DiomKBS/Diom-75TK-legacy/Backplate/depositphotos_342383522-stock-illus.webp

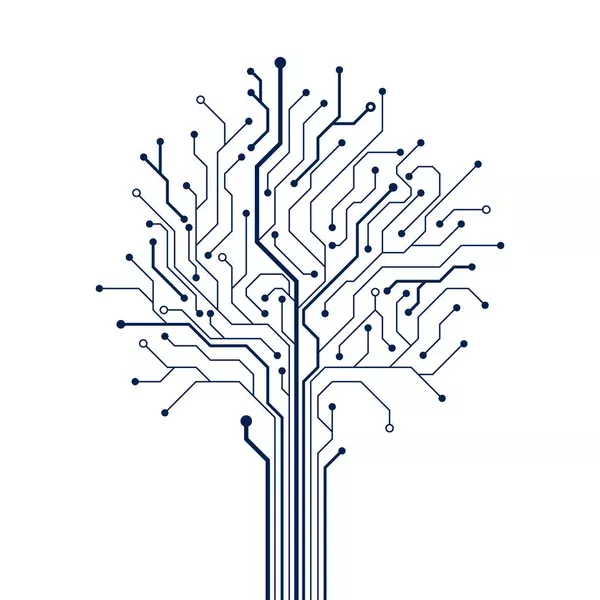
Backplate/depositphotos_342383522-stock-illus.webp
